schaffbar/kassensystem/ArduinoIDE_libraries/Adafruit_ImageReader_Library/images/adabot320x170.bmp

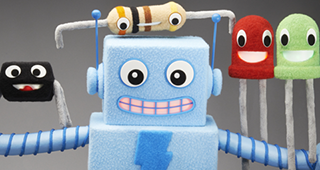
ArduinoIDE_libraries/Adafruit_ImageReader_Library/images/adabot320x170.bmp
