schaffbar/kassensystem/ArduinoIDE_libraries/Adafruit_ImageReader_Library/images/adabot240.bmp

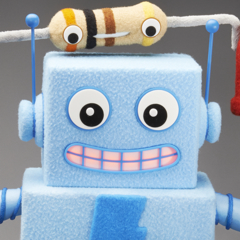
ArduinoIDE_libraries/Adafruit_ImageReader_Library/images/adabot240.bmp
