schaffbar/kassensystem/ArduinoIDE_libraries/Adafruit_ImageReader_Library/images/adabot240x135.bmp

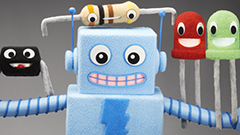
ArduinoIDE_libraries/Adafruit_ImageReader_Library/images/adabot240x135.bmp
