schaffbar/kassensystem/ArduinoIDE_libraries/Adafruit_ImageReader_Library/images/adabot.bmp

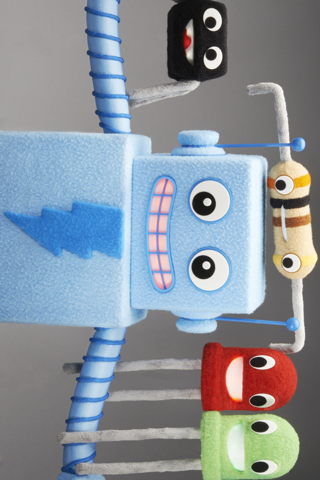
ArduinoIDE_libraries/Adafruit_ImageReader_Library/images/adabot.bmp
