schaffbar/kassensystem/ArduinoIDE_libraries/Adafruit_ImageReader_Library/images/blinka.bmp

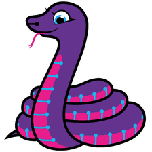
ArduinoIDE_libraries/Adafruit_ImageReader_Library/images/blinka.bmp
