schaffbar/kassensystem/ArduinoIDE_libraries/Adafruit_ImageReader_Library/images/E-Ink 1.54/blinka.bmp

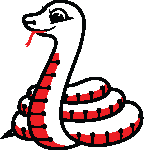
ArduinoIDE_libraries/Adafruit_ImageReader_Library/images/E-Ink 1.54/blinka.bmp
