schaffbar/kassensystem/ArduinoIDE_libraries/Adafruit_ImageReader_Library/images/E-Ink Grayscale 2.9/29gray4.bmp

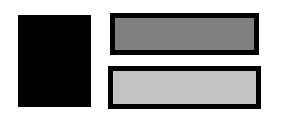
ArduinoIDE_libraries/Adafruit_ImageReader_Library/images/E-Ink Grayscale 2.9/29gray4.bmp
