schaffbar/kassensystem/ArduinoIDE_libraries/Adafruit_ImageReader_Library/images/E-Ink Grayscale 2.9/panda_head.bmp

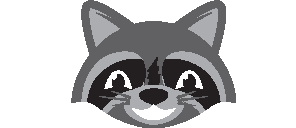
ArduinoIDE_libraries/Adafruit_ImageReader_Library/images/E-Ink Grayscale 2.9/panda_head.bmp
