schaffbar/kassensystem/ArduinoIDE_libraries/Adafruit_ImageReader_Library/images/E-Ink Mono 2.13/blinka.bmp

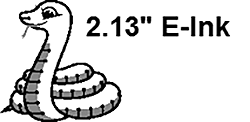
ArduinoIDE_libraries/Adafruit_ImageReader_Library/images/E-Ink Mono 2.13/blinka.bmp
