schaffbar/kassensystem/ArduinoIDE_libraries/Adafruit_ImageReader_Library/images/E-Ink TriColor 2.9/blinka.bmp

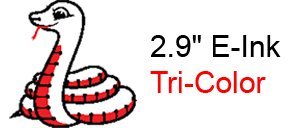
ArduinoIDE_libraries/Adafruit_ImageReader_Library/images/E-Ink TriColor 2.9/blinka.bmp
