schaffbar/kassensystem/ArduinoIDE_libraries/Adafruit_ImageReader_Library/images/E-Ink TriColor 2.13/blinka_hd.bmp

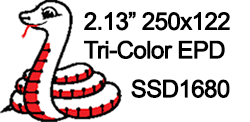
ArduinoIDE_libraries/Adafruit_ImageReader_Library/images/E-Ink TriColor 2.13/blinka_hd.bmp
