schaffbar/kassensystem/ArduinoIDE_libraries/Adafruit_ImageReader_Library/images/lily128.bmp

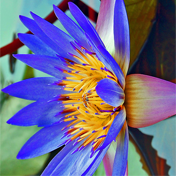
ArduinoIDE_libraries/Adafruit_ImageReader_Library/images/lily128.bmp
