schaffbar/kassensystem/ArduinoIDE_libraries/Adafruit_ImageReader_Library/images/minerva.bmp

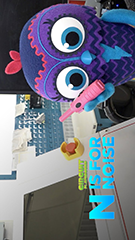
ArduinoIDE_libraries/Adafruit_ImageReader_Library/images/minerva.bmp
