schaffbar/kassensystem/ArduinoIDE_libraries/Adafruit_ImageReader_Library/images/miniwoof.bmp

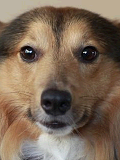
ArduinoIDE_libraries/Adafruit_ImageReader_Library/images/miniwoof.bmp
