schaffbar/kassensystem/ArduinoIDE_libraries/Adafruit_ImageReader_Library/images/purple.bmp

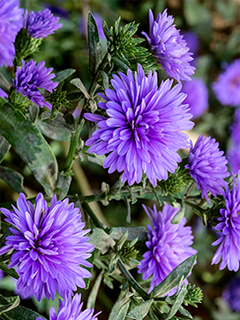
ArduinoIDE_libraries/Adafruit_ImageReader_Library/images/purple.bmp
