schaffbar/kassensystem/ArduinoIDE_libraries/Adafruit_ImageReader_Library/images/rgbwheel.bmp

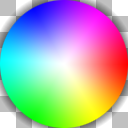
ArduinoIDE_libraries/Adafruit_ImageReader_Library/images/rgbwheel.bmp
