schaffbar/kassensystem/ArduinoIDE_libraries/RAK14014-FT6336U/assets/rakstar.jpg

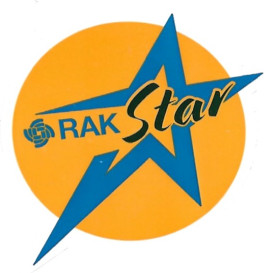
ArduinoIDE_libraries/RAK14014-FT6336U/assets/rakstar.jpg
