schaffbar/kassensystem/ArduinoIDE_libraries/RFID_MFRC522v2/doc/fritzing/Arduino-Uno-r3-with-RFID-RC522.png

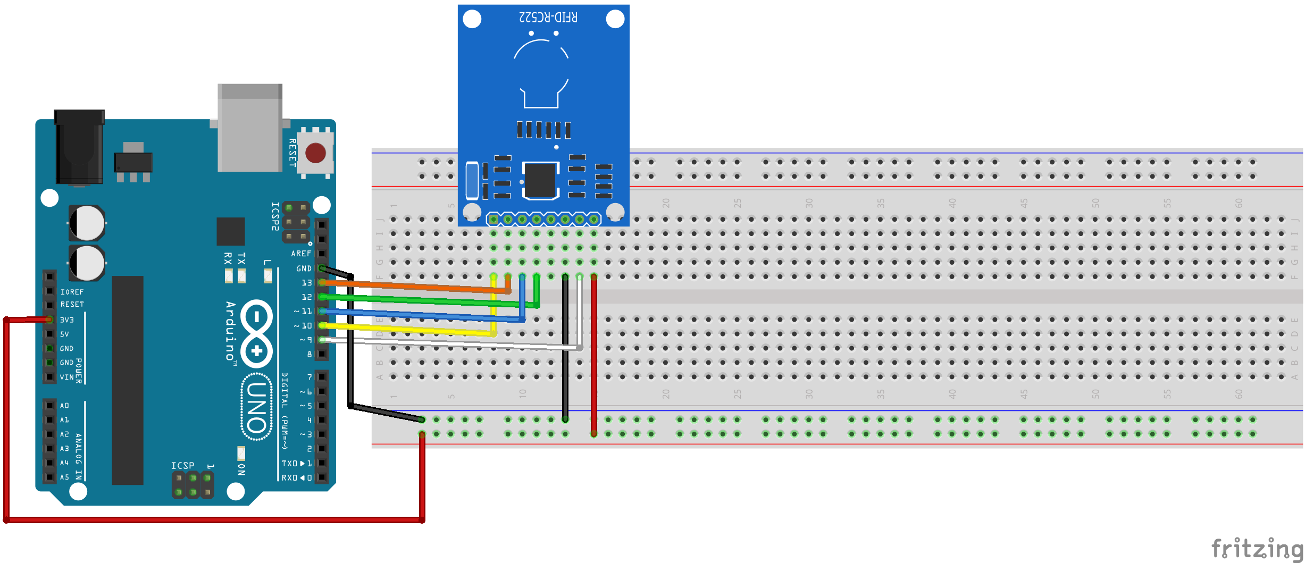
ArduinoIDE_libraries/RFID_MFRC522v2/doc/fritzing/Arduino-Uno-r3-with-RFID-RC522.png
