schaffbar/kassensystem/ArduinoIDE_libraries/RFID_MFRC522v2/doc/fritzing/RFID-RC522-v3.png

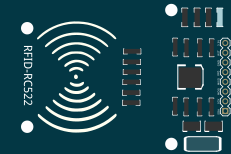
ArduinoIDE_libraries/RFID_MFRC522v2/doc/fritzing/RFID-RC522-v3.png
