schaffbar/kassensystem/ArduinoIDE_libraries/Adafruit_EPD/examples/acep_7ColorTest/adabot.bmp

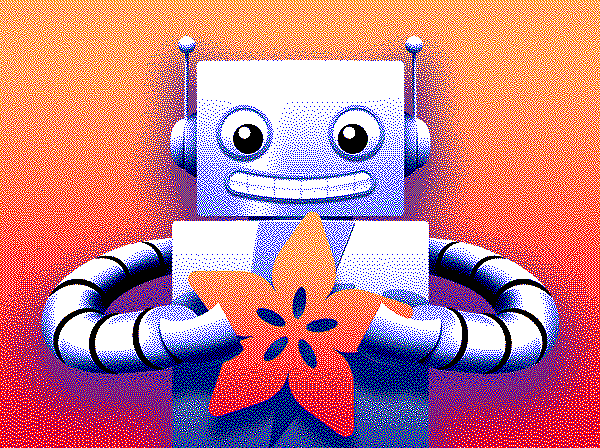
ArduinoIDE_libraries/Adafruit_EPD/examples/acep_7ColorTest/adabot.bmp
