schaffbar/kassensystem/ArduinoIDE_libraries/Adafruit_EPD/examples/acep_7ColorTest/adafruit_characters.bmp

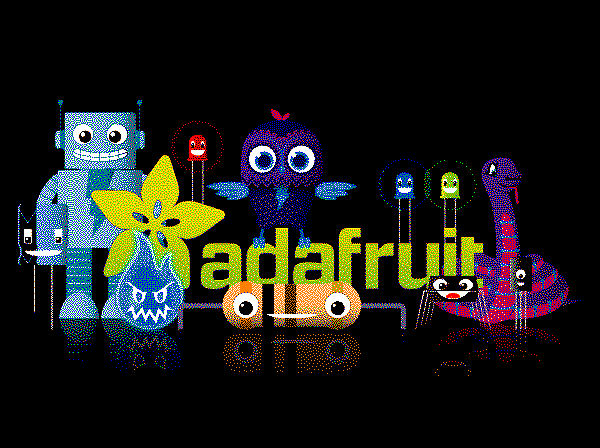
ArduinoIDE_libraries/Adafruit_EPD/examples/acep_7ColorTest/adafruit_characters.bmp
