schaffbar/kassensystem/rfidReader_ArduinoIDE/rfidReader/ver.h

// version history  

const char* sw_version = "0.5.2 beta";

/* 
 * Reihenfolge major.minor.bugfix
 *
 * 0.5.2
 * -) für die UseCases GateKeeper In/Out die Darstellung der Units und Sekunden entfernt
 * -) für die zuvor genannten UseCases den Tag aus der JSon-Struktur entfernt,
 *    die Unit werden jetzt nicht mehr vom Server erwartet und ausgewertet.
 *
 * 0.5.1
 * -) in der evalCounterResp() im else-Pfad das darzustellende Icon gesetzt
 *
 * neuste Änderungen sollen an den Beginn der Liste geschrieben werden
 * 0.5.0
 * -) Aufteilung des UseCases GateKeeper in GateKeeper-In und GateKeeper-Out
 *    Verwendung von getrennten rfidReadern für CheckIn und CheckOut, 
 *    man verspricht sich eine einfachere Erkennung und Behebung von CheckIn/CheckOut-Problemen 
 * -) stop() durch softReset() ersetzt, wenn problematische Json-Files oder unerwartete UsCase-Daten empfangen werden,
 *    da mehr Robustheit gefordert wird, stop() sollte eigentlich zum gemeinsamen Debugging verwendet werden 
 * -) Aufgrund der Konzeptänderung, das keine Zwischenablage (als Datenbankfeld)  mehr verwendet wird und
 *    sondern der Kundeneintrag in der Datenbank auf dem Server zuerst auf "Pending" gesetzt wird und
 *    dann erst das rfid-Tag gelesn wird, wird die id dem Kunden im Zustand "Pending" zugeordnet, 
 *    beide Angaben NAme und ID sollen dann auf dem Display des rfid-Readers dargestellt werden
 * -) Servernamen an die Ausgabe der SWVersion beim Start hinzugefügt
 *
 * 0.4.0
 * -) Wechsel von Raw-Package Kommunikation zu HTTP-Requests
 *    damit kann eine einheitliche SW für die Kommunikation mit den ESP32-Prozessoren und 
 *    dem Web-Frontend am Counter oder anderen Positionen erfolgen.
 *    In der Datrei rfidReader.ino gibt es ein #define RawComFlag  
 *    0 - HTTP-Kommunikation
 *    1 - RawPackage-Kommunikation
 * -) Sleep-Mode-Handling wurde vorbereite ist aber aktuell auskommentiert 
 *
 * 0.3.3 
 * -) Server- und Netzwerkdaten in eine extra Datei verlagert
 *
 * 0.3.2
 * -) UseCase AddTag im State Idle den Wechsel zwischen den rfid und dem UseCase-Bild berichtigt
 *
 * 0.3.1
 * -) In getUseCase die Abkürzung "A" ersetzt jetzt "AddTag"
 *
 * 0.3.0
 * -) Implementierung des UseCase "AddTag" (A), damit die rfidTags in die Card-Tabelle eingelesen 
 *    werden können und ein geschlossener Pool an IDs zur Verfügung steht
 *
 * 0.2.1
 * -) erneuter Aufbau des Breadboards - Anpassung der vorhergehenden Pin-Defintiotionen
 * -) kleine Änderungen bzgl der Tonausgabe, wenn die Antwort vom Server kommt 
 *
 * 0.2.0
 * -) UseCase SwitchBox implementiert, 
 *     bei positiver Rückmeldung vom Server wird über das Funkrelais die Stromversorgung für das Werkzeug eingeschaltet 
 *     und bei der Abmeldung auch wieder ausgeschaltet. *

 * 0.1.1
 * -) in der Datei support.ino in der Funktion void evalTouchAction() = ersetzt durch == 
 *    und ebenfalls den UseCase Counter hinzugefügt
 *
 * 0.1.0
 * -) Darstellung der SW Version beim Start des rfidReaders
 * -) Für den UseCase "GateKeeper", ist es möglich mit "Weiter mit Touch" die Darstellung abzubrechen, damit ein Stau von Kunden vor dem Gerät vermieden wird 
 *
 * 0.0.0 allgemeiner Ansatz
 * Beinhaltet folgende UseCases 
 * -) Counter     Übertragung der RFID in eine Tabelle der Datenbank für die Registrierung am Tresen
 * -) Gatekeeper  Zeiterfassung für den Kunden wie lange er sich im Werkstattbereich aufhält 
 */
